dchwebb/Punck/Punck/src/reverb.h

/* Based on original code by Geraint Luff
 * https://signalsmith-audio.co.uk/writing/2021/lets-write-a-reverb/
 */
#pragma once

#include "initialisation.h"
#include "Filter.h"
#include <cstring>

extern float reverbMixBuffer[94000];

struct DelayLines {
	float* delay;							// pointer to location of samples in delay buffer
	size_t size;							// size of delay buffer
	uint32_t writePos;						// current sample write position
	uint32_t readPos;						// current sample read position

	void write(float sample) {
		delay[writePos++] = sample;
		if (writePos == size) writePos = 0;
		readPos = writePos + 1;				// delay length is constant so always one past the write position
		if (readPos == size) readPos = 0;
	}
};


// Usage: `Householder<double, 8>::inPlace(data)` - size must be ≥ 1
template<uint32_t size>
class Householder {
	static constexpr float multiplier = -2.0f / size;
public:
	static void InPlace(float* arr) {
		float sum = 0.0f;
		for (uint32_t i = 0; i < size; ++i) {
			sum += arr[i];
		}

		sum *= multiplier;

		for (uint32_t i = 0; i < size; ++i) {
			arr[i] += sum;
		}
	};
};


// Usage: `Hadamard<float, 8>::inPlace(data)` - size must be a power of 2
template<typename Sample, int size>
class Hadamard {
public:
	static inline void RecursiveUnscaled(Sample* data) {
		if (size <= 1) {
			return;
		}
		constexpr uint32_t hSize = size / 2;

		// Two (unscaled) Hadamards of half the size
		Hadamard<Sample, hSize>::RecursiveUnscaled(data);
		Hadamard<Sample, hSize>::RecursiveUnscaled(data + hSize);

		// Combine the two halves using sum/difference
		for (uint32_t i = 0; i < hSize; ++i) {
			float a = data[i];
			float b = data[i + hSize];
			data[i] = a + b;
			data[i + hSize] = a - b;
		}
	}

	static inline void inPlace(Sample* data) {
		RecursiveUnscaled(data);

		Sample scalingFactor = std::sqrt(1.0 / size);
		for (uint32_t c = 0; c < size; ++c) {
			data[c] *= scalingFactor;
		}
	}
};



template<int channels = 8>
class DiffuserStep {
public:

	DiffuserStep()
	{
		memset(delayBuffer, 0, sizeof(delayBuffer));			// Clear delay line buffer
		delays[0].delay = &delayBuffer[0];

		// Generate array of randomised delay lengths distributed semi-evenly across the diffusion time
		for (uint32_t i = 0; i < channels; ++i) {
			const float rangeLow = delaySamplesRange * i / channels;
			const float rangeHigh = delaySamplesRange * (i + 1) / channels;
			delays[i].size = std::max(static_cast<uint32_t>(rangeLow +  (rand() / float(RAND_MAX)) * (rangeHigh - rangeLow)), 10UL);

			// Set the start pointer to the start of the current delay line within the combined delay buffer
			if (i < channels) {
				delays[i + 1].delay = delays[i].delay + delays[i].size;
			}
			delays[i].writePos = 0;

			flipPolarity[i] = (rand() & 1);
		}
	}


	std::array<float, channels> Process(const std::array<float, channels>& input)
	{
		std::array<float, channels> output;
		for (uint32_t c = 0; c < channels; ++c) {
			delays[c].write(input[c]);							// Write current sample into delay line
			output[c] = delays[c].delay[delays[c].readPos];		// Read out oldest delayed sample
		}

		Hadamard<float, channels>::inPlace(output.data());		// Mix with a Hadamard matrix

		for (uint32_t c = 0; c < channels; ++c) {				// Flip polarities according to randomised table
			if (flipPolarity[c]) {
				output[c] *= -1;
			}
		}
		return output;
	}

private:
	static constexpr float delayMsRange = 50;
	static constexpr float delaySamplesRange = delayMsRange * 0.001 * systemSampleRate;		// 2400 at 48kHz

	// Create a buffer to hold delay samples - the length of each delay line randomised but grouped in ascending sizes
	// For 8 channels with a delay range of 50ms this means each delay line will a random number partitioned thusly:
	// | 0 - 300 | 300 - 600 | 600 - 900 | 900 - 1200 | 1200 - 1500 | 1500 - 1800 | 1800 - 2100 | 2100 - 2400 |
	float delayBuffer[static_cast<uint32_t>(delaySamplesRange * (channels + 1) / 2)];

	// Hold randomised list of channels to flip polarity of when mixing
	std::array<bool, channels> flipPolarity;

	DelayLines delays[channels];
};



class Reverb;

template<int channels = 8>
class MixedFeedback {
	friend Reverb;
public:
	MixedFeedback()
	{
		memset(reverbMixBuffer, 0, sizeof(reverbMixBuffer));		// Clear delay line buffer
		delays[0].delay = reverbMixBuffer;

		// Generate arrays within delay buffer of increasing delay lengths distributed up from baseDelayLength
		for (uint32_t i = 0; i < channels; ++i) {
			float r = static_cast<float>(i) / channels;
			delays[i].size = static_cast<uint32_t>(std::pow(2.0f, r) * baseDelayLength);

			// Set the start pointer to the start of the current delay line within the combined delay buffer
			if (i < channels) {
				delays[i + 1].delay = delays[i].delay + delays[i].size;
			}
			delays[i].writePos = 0;
			delays[i].readPos = 1;
		}
	}


	void SetDelay(float delay) {
		// Update the size of the delay lines without changing the pointer start positions
		if (delay != delayMs) {
			delayMs = delay;
			for (uint32_t i = 0; i < channels; ++i) {
				const float baseLength = delay * 0.001f * systemSampleRate;		// 150 * .001 * 48000 = 7200
				float r = static_cast<float>(i) / channels;
				delays[i].size = static_cast<uint32_t>(std::pow(2.0f, r) * baseLength);
				delays[i].writePos = 0;
				delays[i].readPos = 1;
			}
		}
	}

	std::array<float, channels> Process(const std::array<float, channels>& input)
	{
		std::array<float, channels> output;
		for (uint32_t c = 0; c < channels; ++c) {
			output[c] = delays[c].delay[delays[c].readPos];			// Read out oldest delayed sample
		}

		Householder<channels>::InPlace(output.data());				// Mix using a Householder matrix

		for (uint32_t c = 0; c < channels; ++c) {
			float sum = input[c] + output[c] * decayGain;
			delays[c].write(sum);									// Write current sample into delay line
		}
		return output;
	}


private:
	static constexpr float maxDelayMs = 150.0f;						// Sets size of delay buffer
	static constexpr float decayGain = 0.75f;
	static constexpr float baseDelayLength = maxDelayMs * 0.001f * systemSampleRate;		// 150 * .001 * 48000 = 7200

	float delayMs = maxDelayMs;

	DelayLines delays[channels];
};



class Reverb {
public:
	Reverb()
	{
		filter.SetCutoff(config.filterCutoff);
	}


	std::pair<float, float> Process(float sampleL, float sampleR) {
		sampleL = filter.CalcFilter(sampleL, channel::left);
		sampleR = filter.CalcFilter(sampleR, channel::right);
		std::array<float, delayChannels> samples {sampleL, sampleR, sampleL, sampleR, sampleL, sampleR, sampleL, sampleR};

		// Generate short diffusion
		for (uint8_t i = 0; i < config.diffuserCount; ++i) {
			samples = diffuserStep[i].Process(samples);
		}

		// Generate long tails with feedback mixer
		if (mixerChannels > 0.0f) {
			samples = feedbackMixer.Process(samples);
		}

		if (mixerChannels == 4.0f) {
			return {(samples[0] + samples[2]) * config.reverbLevel,
				    (samples[1] + samples[3]) * config.reverbLevel};
		} else {
			return {(samples[0] + samples[2] + samples[4] + samples[6]) * config.reverbLevel,
				    (samples[1] + samples[3] + samples[5] + samples[7]) * config.reverbLevel};
		}

	}

	uint32_t SerialiseConfig(uint8_t** buff)
	{
		*buff = reinterpret_cast<uint8_t*>(&config);
		return sizeof(config);
	}


	uint32_t StoreConfig(uint8_t* buff)
	{
		if (buff != nullptr) {
			memcpy(&config, buff, sizeof(config));
		}

		// Verify settings and update as required
		config.diffuserCount = std::clamp(std::round(config.diffuserCount), 0.0f, static_cast<float>(maxDiffusers));
		config.mixerBaseDelay = std::clamp(std::round(config.mixerBaseDelay), 20.0f, static_cast<float>(feedbackMixer.maxDelayMs));
		if ((config.mixerChannels == 0.0f || config.mixerChannels == 4.0f || config.mixerChannels == 8.0f)) {
			mixerChannels = static_cast<uint32_t>(config.mixerChannels);
		}
		feedbackMixer.SetDelay(config.mixerBaseDelay);
		filter.SetCutoff(config.filterCutoff / (systemSampleRate / 2));

		return sizeof(config);
	}

private:
	static constexpr uint32_t maxDiffusers = 3;
	static constexpr uint32_t delayChannels = 8;

	DiffuserStep<delayChannels> diffuserStep[maxDiffusers];
	MixedFeedback<delayChannels> feedbackMixer;
	Filter<2> filter{filterPass::LowPass, nullptr};
	uint32_t mixerChannels = 8;

	struct Config {
		float reverbLevel = 0.01f;							// Wet reverb Level
		float mixerBaseDelay = 75.0f;						// Starting delay of feedback mixer
		float diffuserCount = 2.0f;							// Number of active diffusers
		float mixerChannels = 8.0f;							// 0, 4 or 8 feedback mixer channels
		float filterCutoff = 2400.0f;						// Cutoff in Hertz
	} config;
};


extern Reverb reverb;
