dchwebb/Punck/Punck/src/interrupts.h

void OTG_FS_IRQHandler(void)
{
	usb.InterruptHandler();
}


// Detailed debug timings
uint32_t loopTime = 0, maxLoopTime = 0, outputTime = 0, maxOutputTime = 0, reverbTime = 0, maxReverbTime = 0;


void SPI2_IRQHandler()									// I2S Interrupt
{

#if (TIMINGDEBUG)
	loopTime = TIM3->CNT;
	if (loopTime > maxLoopTime && SysTickVal > 100) {
		maxLoopTime = loopTime;
	}
	TIM3->EGR |= TIM_EGR_UG;							// Re-initialize debug counter
#endif

	if ((SPI2->SR & SPI_SR_UDR) == SPI_SR_UDR) {		// Check for Underrun condition
		SPI2->IFCR |= SPI_IFCR_UDRC;					// Clear underrun condition
		++i2sUnderrun;
		return;
	}

	voiceManager.Output();

#if (TIMINGDEBUG)
	outputTime = TIM3->CNT;
	if (outputTime > maxOutputTime) {
		maxOutputTime = outputTime;
	}
#endif

}


void MDMA_IRQHandler()
{
	// fires when MDMA Flash to memory transfer has completed
	if (MDMA->GISR0 & MDMA_GISR0_GIF0) {
		MDMA_Channel0->CIFCR |= MDMA_CIFCR_CBTIF;		// Clear transfer complete interrupt flag
		usb.msc.DMATransferDone();
	}
}

uint32_t debugUartOR = 0;
void UART8_IRQHandler(void) {
	// MIDI Decoder
	if (UART8->ISR & USART_ISR_RXNE_RXFNE) {
		usb.midi.serialHandler(UART8->RDR); 			// accessing DR automatically resets the receive flag
	} else {
		// Overrun
		UART8->ICR |= USART_ICR_ORECF;					// The ORE bit is reset by setting the ORECF bit in the USART_ICR register
		++debugUartOR;
	}
}

// System interrupts
void NMI_Handler(void) {}

void HardFault_Handler(void) {
	while (1) {}
}
void MemManage_Handler(void) {
	while (1) {}
}
void BusFault_Handler(void) {
	while (1) {}
}
void UsageFault_Handler(void) {
	while (1) {}
}

void SVC_Handler(void) {}

void DebugMon_Handler(void) {}

void PendSV_Handler(void) {}

void SysTick_Handler(void) {
	++SysTickVal;
}

/*
// USART Decoder
void USART3_IRQHandler() {
	//if ((USART3->ISR & USART_ISR_RXNE_RXFNE) != 0 && !uartCmdRdy) {
	if (!uartCmdRdy) {
		uartCmd[uartCmdPos] = USART3->RDR; 				// accessing RDR automatically resets the receive flag
		if (uartCmd[uartCmdPos] == 10) {
			uartCmdRdy = true;
			uartCmdPos = 0;
		} else {
			uartCmdPos++;
		}
	}
}*/
